EntropicEngineering/vestibular_vampire/software/20hz_demo/20hz_demo.ino

#include <Wire.h>
#include <Adafruit_MCP4725.h>
#include <math.h>

#define SDA_PIN 14
#define SCL_PIN 15
#define DAC_ADDRESS 0x62

//Startup delay, (ms).
#define STARTUP_DELAY 3000

Adafruit_MCP4725 dac;

#define DAC_RESOLUTION    (4096)   
#define OFFSET            (2048)   
#define AMPLITUDE         (512)    
#define NUM_POINTS        (128)  
float offsetX = 0.04;  
int Correct = 0;

void setup(void)
{
  //Set the I2C pins.
  Wire1.setSDA(SDA_PIN);
  Wire1.setSCL(SCL_PIN);
  Wire1.begin();
  Wire.setClock(400000);   
  dac.begin(DAC_ADDRESS, &Wire1);  
  Correct = mapFloat(offsetX, -4.0, 4.0, 0, 4095);

  //Set the output voltage, but do not persist after power cycle.
  dac.setVoltage(Correct, false);
  delay(STARTUP_DELAY);
}

float linspace(int start, int end, int step, int numSteps)
{
  return start + (float)(end - start) * step / (numSteps - 1);
}

void loop(void)
{
  static bool reachedMaxFrequency = false; 
  static int step = 0;                     
  
  float targetFrequency;
  
  if (!reachedMaxFrequency) {
    targetFrequency = linspace(1, 20, step, 20); 
    
    if (step < 19) {
      step++; 
    } else {
      reachedMaxFrequency = true; 
    }
  } else {
    targetFrequency = 20; 
  }
  
  float sampleRate = targetFrequency * NUM_POINTS;    
  unsigned long delayTime = 1000000 / sampleRate;  

  for (int repeat = 0; repeat < 3; repeat++) {
    unsigned long lastTime = micros();  
    for (uint16_t i = 0; i < NUM_POINTS; i++) {
      float angle = (2 * PI * i) / NUM_POINTS;
      uint16_t voltage = Correct + (AMPLITUDE * sin(angle));

      dac.setVoltage(voltage, false);
      while (micros() - lastTime < delayTime);
      lastTime += delayTime;
    }
  }
}

int mapFloat(float x, float in_min, float in_max, int out_min, int out_max)
{
  return (x - in_min) * (out_max - out_min) / (in_max - in_min) + out_min;
}
